StonedDawg/FENIX-rx5808-pro-diversity/src/src/state_home.h

#ifndef STATE_HOME_H
#define STATE_HOME_H

#include "channels.h"
#include "state.h"
#include "settings.h"
#include "receiver.h"

namespace StateMachine {
    class HomeStateHandler : public StateMachine::StateHandler {
        private:
            void doTapAction();
    
            uint8_t displayActiveChannel = 0;
            uint8_t scanNext = 0;
            uint16_t bandScanSelectedChannel = 0;
            uint8_t menuLevel = 1;
            uint8_t internalSelectedMenu = 0;
            bool wasInBandScanRegion = false;
            bool isInBandScanRegion();
            bool isInAnalyzeRegion();
            void bandScanUpdate();
            
            void setChannel(int channelIncrement);
            void centreFrequency();
            bool centred = false;
            
            uint8_t orderedChanelIndex = 0;
            uint8_t lastChannelIndex = 0;

        public:
            
            void onEnter();
            void onUpdate();

            void onInitialDraw();
            void onUpdateDraw();
    };
}

#endif
