StonedDawg/FENIX-rx5808-pro-diversity/src/src/state_settings_rssi.h

#ifndef STATE_SETTINGS_RSSI_H
#define STATE_SETTINGS_RSSI_H


#include "state.h"


namespace StateMachine {
    class SettingsRssiStateHandler : public StateMachine::StateHandler {
        private:
            enum class InternalState : uint8_t {
                WAIT_FOR_LOW,
                SCANNING_LOW,
                WAIT_FOR_HIGH,
                SCANNING_HIGH,
                DONE,
                IDLE
            };

            void doTapAction();

            InternalState internalState = InternalState::WAIT_FOR_LOW;
            uint8_t currentSweep = 0;
            uint8_t sweepWaitBtn = 0;
            uint8_t bestChannel = 0; 


        public:
            void onEnter();
            void onUpdate();

            void onInitialDraw();
            void onUpdateDraw();

    };
}


#endif
